ecocurious2/MultiGeiger/docs/Bilder/IMG_0659.JPG

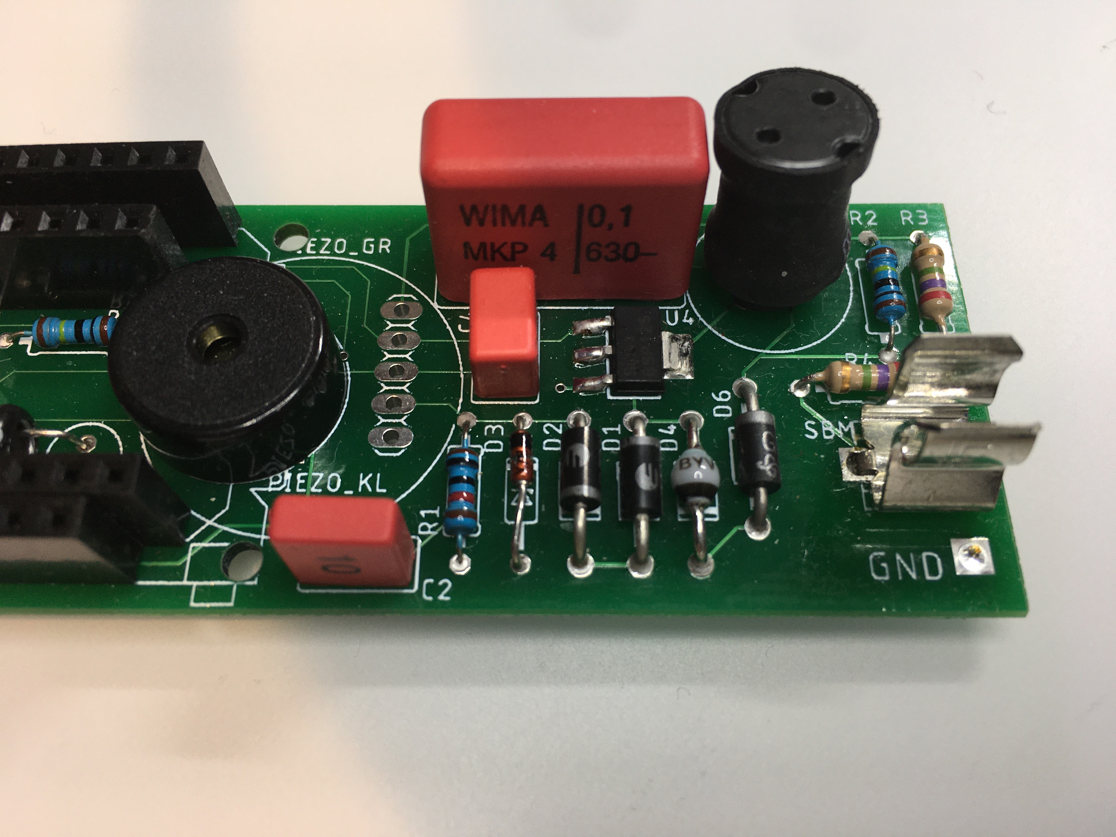
docs/Bilder/IMG_0659.JPG
