ecocurious2/MultiGeiger/docs/Bilder/IMG_0974.JPG

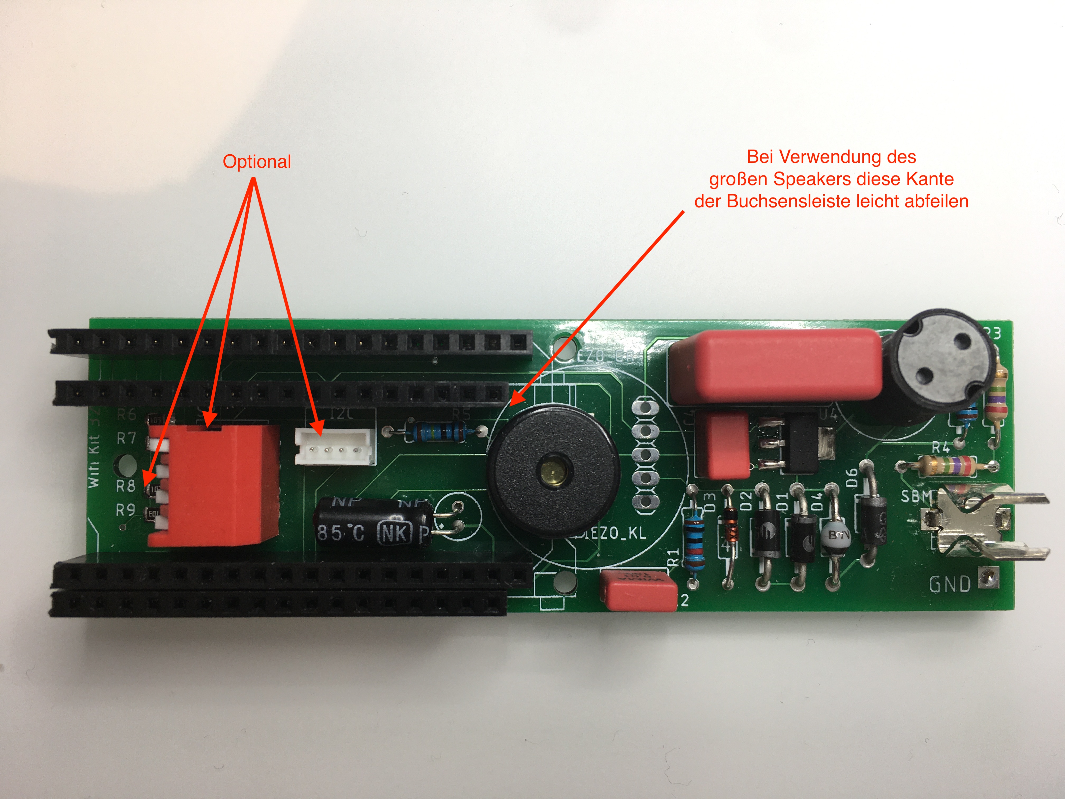
docs/Bilder/IMG_0974.JPG
