ecocurious2/MultiGeiger/docs/Bilder/IMG_5491.JPG

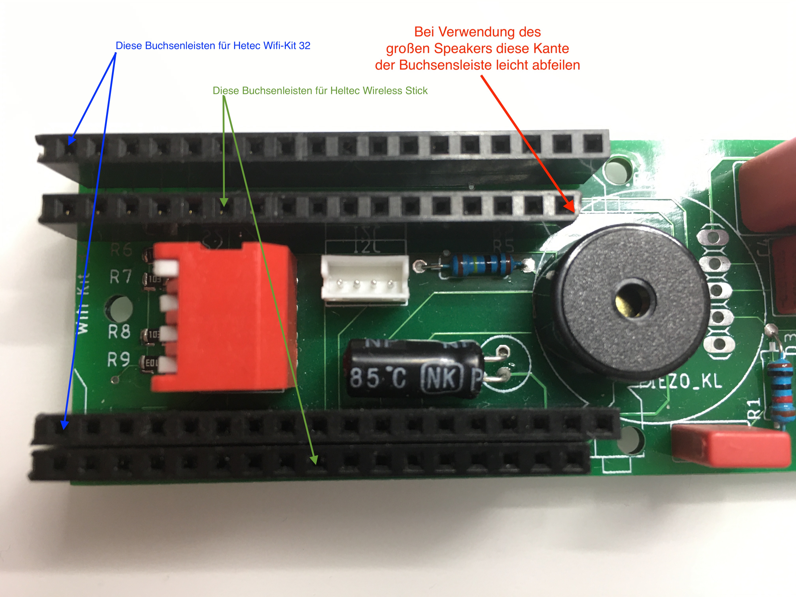
docs/Bilder/IMG_5491.JPG
