ecocurious2/MultiGeiger/docs/Bilder/IMG_8667.JPG

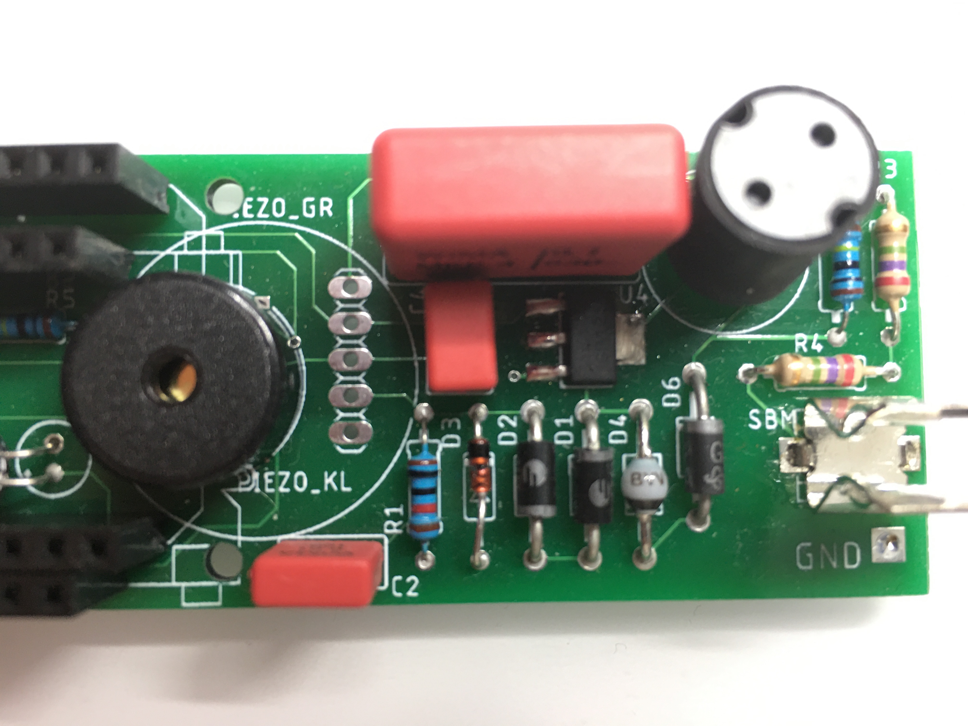
docs/Bilder/IMG_8667.JPG
