ecocurious2/MultiGeiger/docs/source/images/config.png

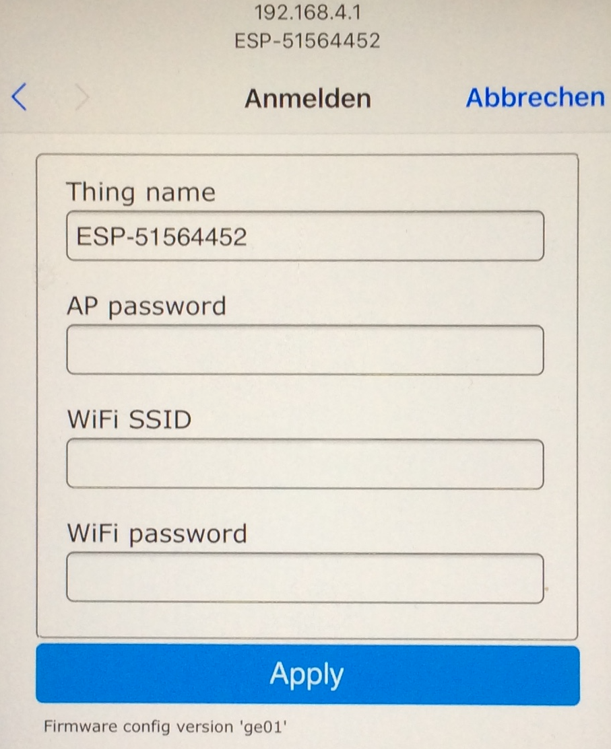
docs/source/images/config.png
