ecocurious2/MultiGeiger/docs/source/images/http_integration_filled.png

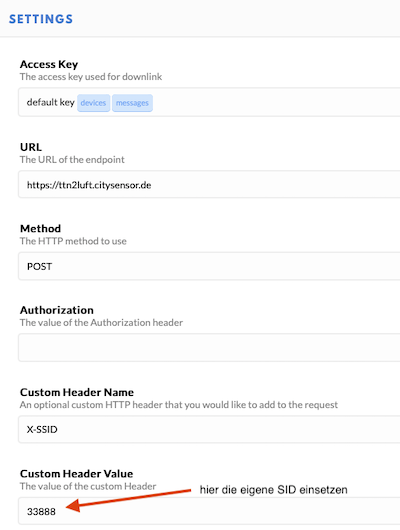
docs/source/images/http_integration_filled.png
