ecocurious2/MultiGeiger/docs/source/images/build_02_parts_all.jpg

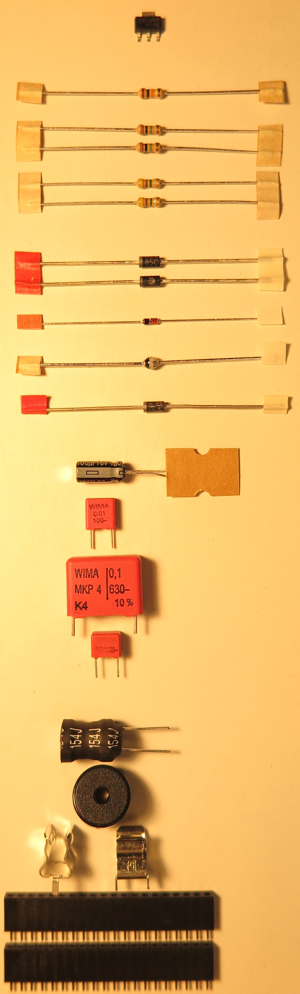
docs/source/images/build_02_parts_all.jpg
