ecocurious2/MultiGeiger/docs/source/images/build_14_bottle_both.jpg

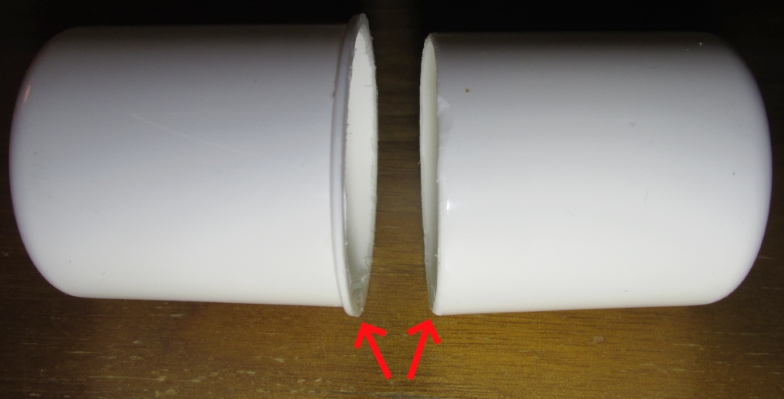
docs/source/images/build_14_bottle_both.jpg
