ecocurious2/MultiGeiger/multigeiger/ca_certs.h

// CA Roots for LetsEncrypt Certificates (cross-signed):
// - 1. ISRG Root X1 - valid until 2035-06-04
// - 2. DST Root CA X3 - valid until 2021-09-30
// CA Roots for Google stuff:
// - 3. GlobalSign Root R1 - valid until 2028-01-28
// CA Root for Amazon stuff:
// - 4. Amazon Root CA 1 - valid until 2038-01-17

char ca_certs[] = R"=====(
-----BEGIN CERTIFICATE-----
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
-----END CERTIFICATE-----
-----BEGIN CERTIFICATE-----
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
-----END CERTIFICATE-----
-----BEGIN CERTIFICATE-----
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
HMUfpIBvFSDJ3gyICh3WZlXi/EjJKSZp4A==
-----END CERTIFICATE-----
-----BEGIN CERTIFICATE-----
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
rqXRfboQnoZsG4q5WTP468SQvvG5
-----END CERTIFICATE-----
)=====";
