ecocurious2/MultiGeiger/multigeiger/clock.cpp

#include <Arduino.h>
#include <sys/time.h>

#include "clock.h"


void config_time(time_t timestamp) {
  if (timestamp > 0) {
    // a specific timestamp was given, e.g. for testing purposes, set time:
    struct timeval tv = {timestamp, 0};
    settimeofday(&tv, nullptr);
  } else {
    // timestamp == 0 means we shall use NTP to get the time:
    configTime(TZ_OFFSET, DST_OFFSET, NTP_SRV_1, NTP_SRV_2);
    // please note that this just sets up NTP. the actual time sync might take some minutes...
  }
}


char *utctime(void) {
  // return a pointer to a timestamp string like 2019-12-31T23:59:59
  time_t t;
  struct tm *ti;
  static char buffer[20];

  time(&t);
  ti = gmtime(&t);
  strftime(buffer, 20, "%Y-%m-%dT%H:%M:%S", ti);
  return buffer;
}


void setup_clock(time_t timestamp) {
  config_time(timestamp);
}
