ecocurious2/MultiGeiger/multigeiger/utils.h

// Misc. utilities

#ifndef UTILS_H
#define UTILS_H

// Prototypes
int hex2data(unsigned char *data, const char *hexstring, unsigned int len);
void reverseByteArray(unsigned char *data, int len);

#endif
